frohlfing/biodom-mini/sketches/JPGtoXBM/JPGtoXBM_PoC_2/frank_128x64_clean_jpg.h

#pragma once

static const unsigned char frank_128x64_clean_jpg[] PROGMEM = {
    0xFF, 0xD8, 0xFF, 0xE0, 0x00, 0x10, 0x4A, 0x46, 0x49, 0x46, 0x00, 0x01, 0x01, 0x01, 0x01, 0x2C, 
    0x01, 0x2C, 0x00, 0x00, 0xFF, 0xE2, 0x02, 0xB0, 0x49, 0x43, 0x43, 0x5F, 0x50, 0x52, 0x4F, 0x46, 
    0x49, 0x4C, 0x45, 0x00, 0x01, 0x01, 0x00, 0x00, 0x02, 0xA0, 0x6C, 0x63, 0x6D, 0x73, 0x04, 0x40, 
    0x00, 0x00, 0x6D, 0x6E, 0x74, 0x72, 0x52, 0x47, 0x42, 0x20, 0x58, 0x59, 0x5A, 0x20, 0x07, 0xE9, 
    0x00, 0x0B, 0x00, 0x07, 0x00, 0x02, 0x00, 0x1B, 0x00, 0x27, 0x61, 0x63, 0x73, 0x70, 0x4D, 0x53, 
    0x46, 0x54, 0x00, 0x00, 0x00, 0x00, 0x00, 0x00, 0x00, 0x00, 0x00, 0x00, 0x00, 0x00, 0x00, 0x00, 
    0x00, 0x00, 0x00, 0x00, 0x00, 0x00, 0x00, 0x00, 0x00, 0x00, 0x00, 0x00, 0xF6, 0xD6, 0x00, 0x01, 
    0x00, 0x00, 0x00, 0x00, 0xD3, 0x2D, 0x6C, 0x63, 0x6D, 0x73, 0x00, 0x00, 0x00, 0x00, 0x00, 0x00, 
    0x00, 0x00, 0x00, 0x00, 0x00, 0x00, 0x00, 0x00, 0x00, 0x00, 0x00, 0x00, 0x00, 0x00, 0x00, 0x00, 
    0x00, 0x00, 0x00, 0x00, 0x00, 0x00, 0x00, 0x00, 0x00, 0x00, 0x00, 0x00, 0x00, 0x00, 0x00, 0x00, 
    0x00, 0x00, 0x00, 0x00, 0x00, 0x00, 0x00, 0x00, 0x00, 0x0D, 0x64, 0x65, 0x73, 0x63, 0x00, 0x00, 
    0x01, 0x20, 0x00, 0x00, 0x00, 0x40, 0x63, 0x70, 0x72, 0x74, 0x00, 0x00, 0x01, 0x60, 0x00, 0x00, 
    0x00, 0x36, 0x77, 0x74, 0x70, 0x74, 0x00, 0x00, 0x01, 0x98, 0x00, 0x00, 0x00, 0x14, 0x63, 0x68, 
    0x61, 0x64, 0x00, 0x00, 0x01, 0xAC, 0x00, 0x00, 0x00, 0x2C, 0x72, 0x58, 0x59, 0x5A, 0x00, 0x00, 
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
    0x00, 0x00, 0x00, 0x03, 0x00, 0x00, 0x00, 0x00, 0xA3, 0xD7, 0x00, 0x00, 0x54, 0x7C, 0x00, 0x00, 
    0x4C, 0xCD, 0x00, 0x00, 0x99, 0x9A, 0x00, 0x00, 0x26, 0x67, 0x00, 0x00, 0x0F, 0x5C, 0x6D, 0x6C, 
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
