frohlfing/biodom-mini/sketches/JPGtoXBM/JPGtoXBM_PoC_1/frank_128x64_xbm.h

#pragma once

/**
 * Mein Portrait aus docs/assets/frank_128x64.jpg im XBM-Format.
 * 
 * Diese Headerdatei ist eine Kopie aus dem include-Verzeichnis,
 * damit die Arduino IDE diese einbinden kann.
 */ 

static const unsigned char frank_128x64_xbm[] PROGMEM = { 
    0x00, 0x00, 0x00, 0xFE, 0xFF, 0x3B, 0xEE, 0x63, 0x4B, 0x00, 0x00, 0x00, 
    0x00, 0x00, 0x00, 0x00, 0x00, 0x00, 0x00, 0xFF, 0xFF, 0x97, 0x5E, 0x0A, 
    0x00, 0x00, 0x00, 0x00, 0x00, 0x00, 0x00, 0x00, 0x00, 0x00, 0x80, 0xDF, 
    0xFD, 0x6B, 0xA7, 0x99, 0x0A, 0x00, 0x00, 0x00, 0x00, 0x00, 0x00, 0x00, 
    0x00, 0x00, 0x80, 0x7F, 0xF3, 0xBC, 0x5B, 0x64, 0x01, 0x00, 0x00, 0x00, 
    0x00, 0x00, 0x00, 0x00, 0x00, 0x00, 0x80, 0x5F, 0xFD, 0xF5, 0x9F, 0xAA, 
    0x00, 0x00, 0x00, 0x00, 0x00, 0x00, 0x00, 0x00, 0x00, 0x00, 0xC0, 0xFF, 
    0xA6, 0xBB, 0x62, 0x56, 0x09, 0x00, 0x00, 0x00, 0x00, 0x00, 0x00, 0x00, 
    0x00, 0x00, 0xC0, 0xBF, 0xFE, 0xBD, 0xAB, 0xAF, 0x00, 0x00, 0x00, 0x00, 
    0x00, 0x00, 0x00, 0x00, 0x00, 0x00, 0xC0, 0x7F, 0x95, 0x8B, 0xDE, 0x6B, 
    0x02, 0x00, 0x00, 0x00, 0x00, 0x00, 0x00, 0x00, 0x00, 0x00, 0xC0, 0x7F, 
    0xAD, 0x87, 0xB7, 0xBF, 0x01, 0x00, 0x00, 0x00, 0x00, 0x00, 0x00, 0x00, 
    0x00, 0x00, 0xE0, 0x7F, 0xC9, 0x76, 0xFF, 0x7F, 0x00, 0x00, 0x00, 0x00, 
    0x00, 0x00, 0x00, 0x00, 0x00, 0x00, 0xE0, 0xFF, 0x5E, 0xEB, 0xFF, 0x7F, 
    0x00, 0x00, 0x00, 0x00, 0x00, 0x00, 0x00, 0x00, 0x00, 0x00, 0xC0, 0xFF, 
    0xA3, 0xF5, 0xFF, 0x7F, 0x00, 0x00, 0x00, 0x00, 0x00, 0x00, 0x00, 0x00, 
    0x00, 0x00, 0xE0, 0xF7, 0x3E, 0xF7, 0xFF, 0x7F, 0x00, 0x00, 0x00, 0x00, 
    0x00, 0x00, 0x00, 0x00, 0x00, 0x00, 0xE0, 0xDF, 0xA9, 0xFC, 0xFF, 0xA6, 
    0x02, 0x00, 0x00, 0x00, 0x00, 0x00, 0x00, 0x00, 0x00, 0x00, 0xE0, 0xFF, 
    0x5B, 0xFD, 0xBF, 0x3B, 0x00, 0x00, 0x00, 0x00, 0x00, 0x00, 0x00, 0x00, 
    0x00, 0x00, 0xD0, 0xB7, 0x9D, 0xFE, 0x7F, 0x08, 0x00, 0x00, 0x00, 0x00, 
    0x04, 0x00, 0x00, 0x00, 0x00, 0x00, 0xF0, 0xDF, 0xD5, 0xFF, 0x6F, 0x08, 
    0x00, 0x00, 0x00, 0x00, 0x01, 0x00, 0x00, 0x00, 0x00, 0x00, 0xF0, 0xFF, 
    0xFD, 0xFF, 0x0F, 0x00, 0x00, 0x00, 0x00, 0x00, 0x00, 0x00, 0x00, 0x00, 
    0x00, 0x00, 0xF8, 0xFF, 0xFE, 0xFF, 0x17, 0x00, 0x00, 0x00, 0x00, 0x00, 
    0x00, 0x00, 0x00, 0x00, 0x00, 0x00, 0xF0, 0xCF, 0xFD, 0xFF, 0x59, 0x01, 
    0x00, 0x00, 0x00, 0x00, 0x00, 0x00, 0x00, 0x00, 0x00, 0x00, 0xF8, 0xBF, 
    0xFF, 0xFF, 0x2B, 0x00, 0x00, 0x00, 0x02, 0x00, 0x00, 0x00, 0x00, 0x00, 
    0x00, 0x00, 0xF0, 0xFF, 0xFF, 0xFF, 0x17, 0x00, 0x00, 0x40, 0x00, 0x00, 
    0x04, 0x00, 0x00, 0x00, 0x00, 0x00, 0xF0, 0xFF, 0xFF, 0xFF, 0x56, 0x00, 
    0x00, 0x40, 0x0A, 0x00, 0x07, 0x00, 0x00, 0x00, 0x00, 0x00, 0xF0, 0xFF, 
    0xFF, 0xFF, 0x2F, 0x00, 0x00, 0xAC, 0x00, 0x80, 0x04, 0x00, 0x00, 0x00, 
    0x00, 0x00, 0xF0, 0xFF, 0xFF, 0xFF, 0x17, 0x00, 0xA0, 0x3A, 0x09, 0xC0, 
    0x08, 0x00, 0x00, 0x00, 0x00, 0x00, 0xE0, 0xFF, 0xFF, 0xFF, 0x6F, 0x02, 
    0x00, 0x41, 0x10, 0xC0, 0x01, 0x00, 0x00, 0x00, 0x00, 0x00, 0x40, 0xFF, 
    0xFF, 0xFF, 0x1F, 0x00, 0x40, 0x61, 0x45, 0xE1, 0x02, 0x00, 0x00, 0x00, 
    0x00, 0x00, 0x40, 0xFF, 0xFF, 0xFF, 0x3F, 0x00, 0x10, 0x00, 0x3C, 0x80, 
    0x00, 0x00, 0x00, 0x00, 0x00, 0x00, 0x80, 0xFE, 0xFF, 0xFF, 0x1F, 0x00, 
    0x15, 0x90, 0xF7, 0x01, 0x01, 0x00, 0x00, 0x00, 0x00, 0x00, 0x80, 0xFF, 
    0xFF, 0xFF, 0x6F, 0x18, 0x08, 0xE0, 0x6F, 0x01, 0x00, 0x00, 0x00, 0x00, 
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
