frohlfing/biodom-mini/sketches/DS18B20_Test/DS18B20_Test.ino

/**
 * Funktionstest für den Bodentemperatursensor DS18B20
 */

#include <OneWire.h>
#include <DallasTemperature.h>

// Data wire is plugged into port 2 on the Arduino
#define ONE_WIRE_BUS 4

// Setup a oneWire instance to communicate with any OneWire devices (not just Maxim/Dallas temperature ICs)
OneWire oneWire(ONE_WIRE_BUS);

// Pass our oneWire reference to Dallas Temperature.
DallasTemperature sensors(&oneWire);

void setup(void) {
    Serial.begin(115200);
    Serial.println("DS18B20 Test");
    sensors.begin();
}

void loop(void) {
    sensors.requestTemperatures();
    delay(1500);
    float tempC = sensors.getTempCByIndex(0);
    if (tempC != DEVICE_DISCONNECTED_C) {
        Serial.print("Temperature:");
        Serial.println(tempC);
    } else {
        Serial.println("Error: Could not read temperature data");
    }
}
