frohlfing/biodom-mini/include/secrets.example.h

#pragma once

/**
 * Sensible Umgebungsdaten (Vorlage für secrets.h)
 */

// Webinterface
constexpr char WIFI_SSID[] = "DEIN_WLAN_NAME";          // WLAN-SSID
constexpr char WIFI_PASSWORD[] = "DEIN_WLAN_PASSWORT";  // WLAN-Passwort
